EnmaAi-0/2.4Ghz-Remote-control-/code/Seekfree_MM32SPIN27PS_Opensource_Library/Project/CODE/system.c

#include "system.h"

int16 Rocker_LX,Rocker_LY,Rocker_RX,Rocker_RY;
float Battery_Power;

void system_init(void)
{
	
	//oled初始化
	oled_init();
	
	//摇杆初始化
	adc_init(ADC_1, ADC1_CH00_A00, ADC_12BIT);
	adc_init(ADC_1, ADC1_CH02_A02, ADC_12BIT);
	adc_init(ADC_1, ADC1_CH03_A03, ADC_12BIT);
	adc_init(ADC_1, ADC1_CH05_A05, ADC_12BIT);
	
	//电量检测
	adc_init(ADC_1, ADC1_CH06_A06, ADC_12BIT);
	
	//2.4G通讯模块 SI24R1初始化
	NRF_Dev_Init();
	
	//按键初始化
	key_init();

	
	
	//用于产生时钟
	tim_interrupt_init_ms(TIM_14,1, 3);
}


void Get_Power(void)		//此处电压换算根据电阻比例计算
{
	Battery_Power=(float)adc_mean_filter(ADC_1, ADC1_CH06_A06,5) * 0.0046385f;
}
