EnmaAi-0/2.4Ghz-Remote-control-/code/Seekfree_MM32SPIN27PS_Opensource_Library/Project/CODE/system.h

#ifndef _SYSTEM_H_
#define _SYSTEM_H_

#include "headfile.h"


extern int16 Rocker_LX,Rocker_LY,Rocker_RX,Rocker_RY;
extern float Battery_Power;

void system_init(void);
void Get_Power(void);



#endif
